OPRobots/IRStart/source_code/Remote/include/pinout.h

#ifndef PINOUT_H
#define PINOUT_H

#define LED 8
#define NEOPIXEL 5
#define BAT_ANALOG 2

#define IR_CMD 4
#define IR_CMD_PWM 0
#define IR_PROG 7
#define IR_PROG_PWM 1

#define BTN_START 21
#define BTN_STOP 20
#define BTN_READY 10
#define BTN_MODE 6

#define DIP_SW_0 0
#define DIP_SW_1 1
#define DIP_SW_2 2
#define DIP_SW_3 3

#endif
